fc0076/MeteoJet/3D_parts/printer/Stripled - Supports.3mf

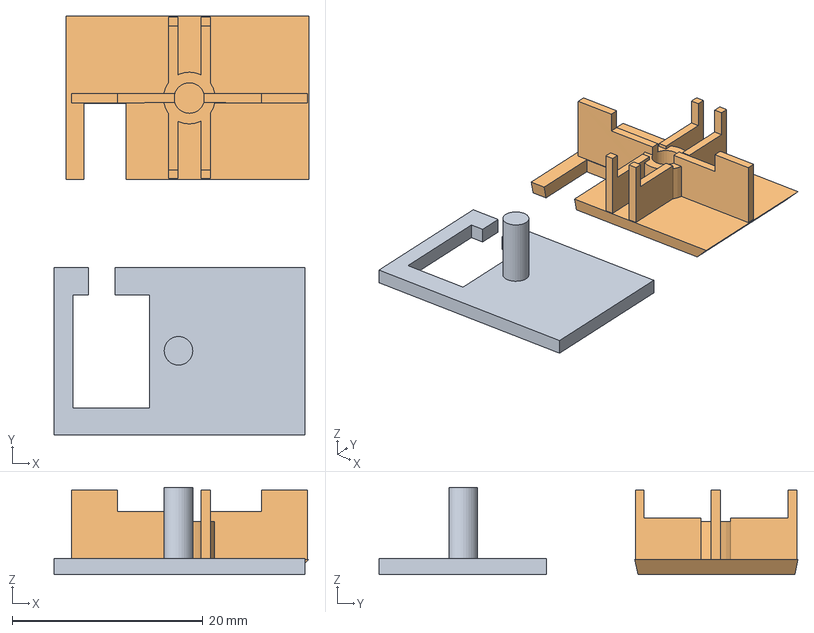
[picture p38: CAD file, 2026-04-10]
3D_parts/printer/Stripled - Supports.3mf
26.7 x 43.9 x 9.15 mm
Stripled - Bottom support.stl
Stripled - Top support.stl
