fc0076/MeteoJet/3D_parts/objects/Stripled - Bottom support.stl

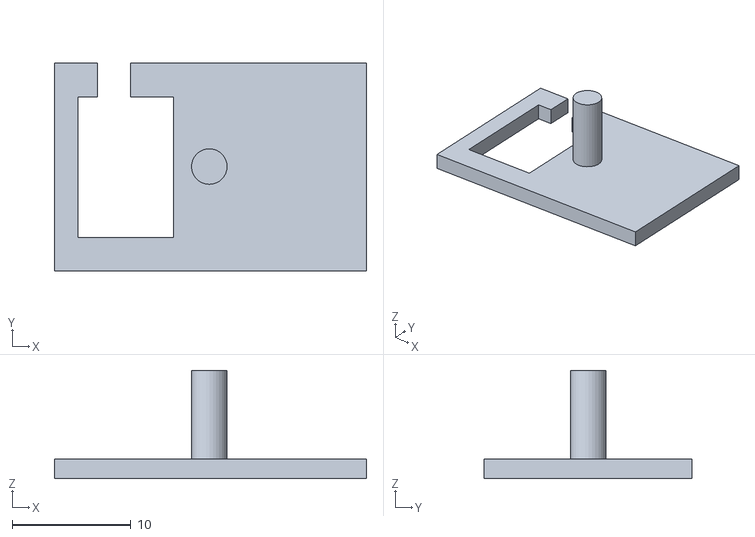
[picture p39: CAD file, 2026-04-10]
3D_parts/objects/Stripled - Bottom support.stl
26.3 x 17.6 x 9.15
