fc0076/MeteoJet/3D_parts/printer/Rain gauge - Tank.3mf

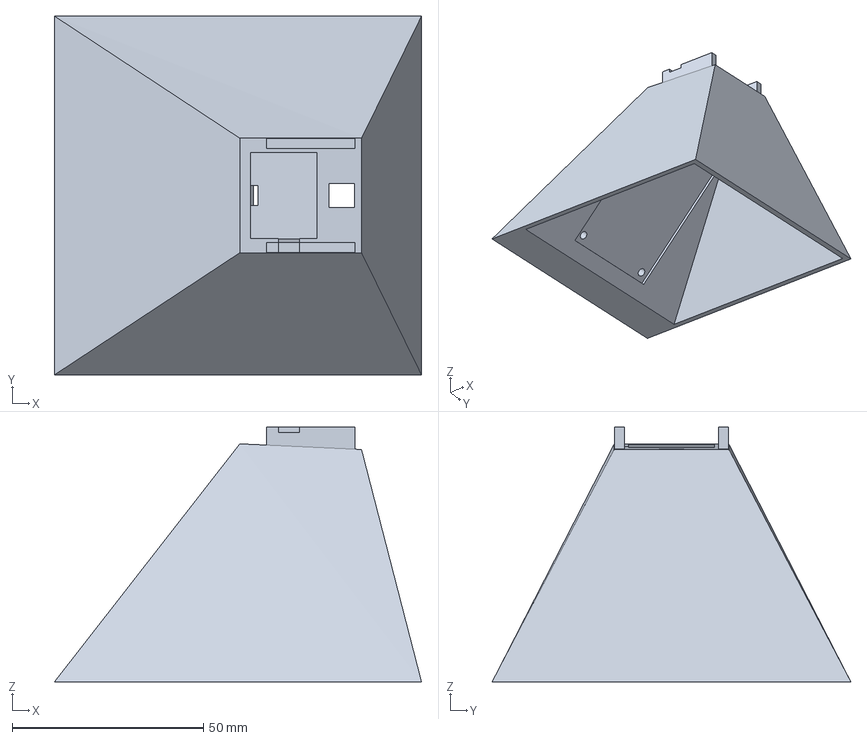
[picture p40: CAD file, 2026-04-10]
3D_parts/printer/Rain gauge - Tank.3mf
96.1 x 93.9 x 66.6 mm
