fc0076/MeteoJet/3D_parts/objects/Support - Arm.stl

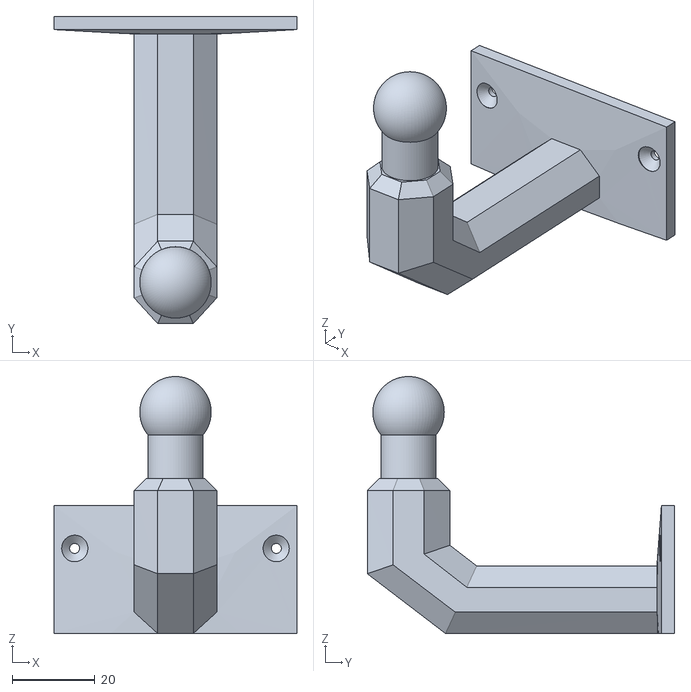
[picture p41: CAD file, 2026-04-10]
3D_parts/objects/Support - Arm.stl
58.9 x 74.5 x 62.3
