fc0076/MeteoJet/3D_parts/printer/Anemometer - Body.3mf

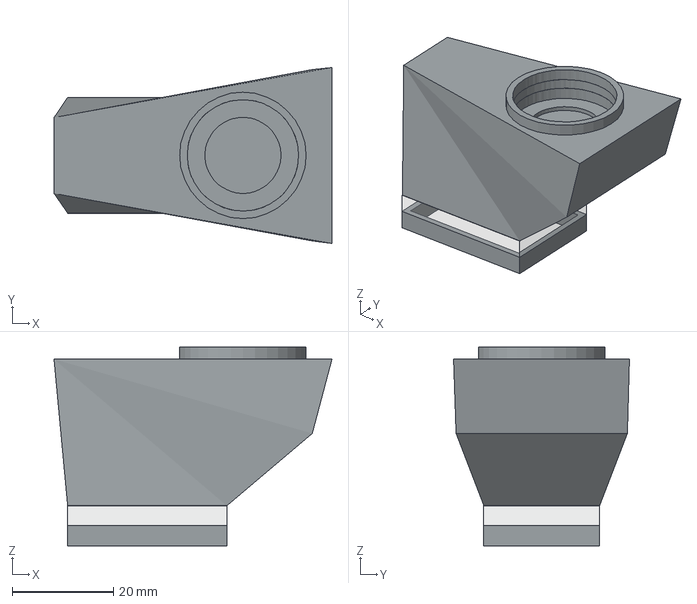
[picture p42: CAD file, 2026-04-10]
3D_parts/printer/Anemometer - Body.3mf
55.0 x 34.8 x 39.3 mm
