fc0076/MeteoJet/3D_parts/objects/Stripled - Top support.stl

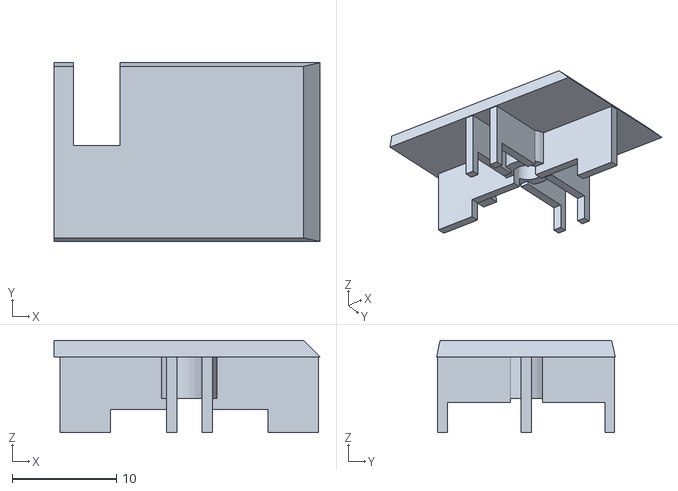
[picture p43: CAD file, 2026-04-10]
3D_parts/objects/Stripled - Top support.stl
25.5 x 17.1 x 8.86
