fc0076/MeteoJet/3D_parts/objects/Stevenson screen - Bottom dome.stl

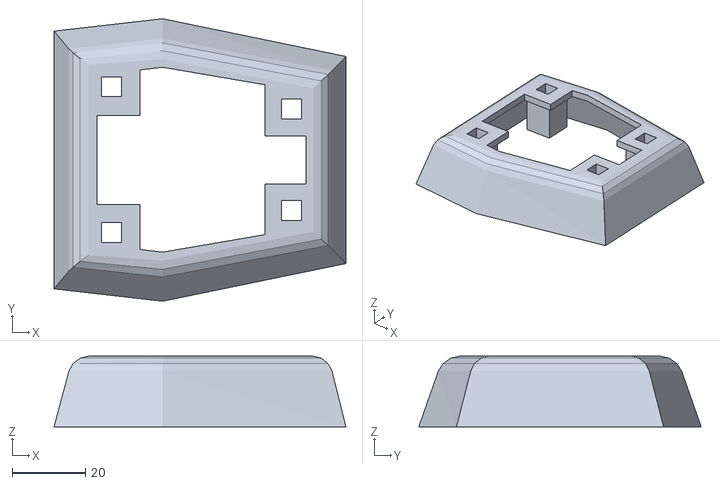
[picture p44: CAD file, 2026-04-10]
3D_parts/objects/Stevenson screen - Bottom dome.stl
79.5 x 76.9 x 19.2
