fc0076/MeteoJet/3D_parts/objects/Support - plate.stl

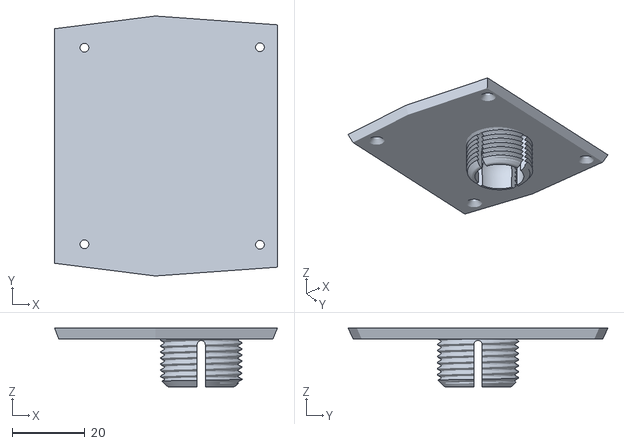
[picture p45: CAD file, 2026-04-10]
3D_parts/objects/Support - plate.stl
61.2 x 71.4 x 16.2
